zenitheesc/Probe-RAS/KiCad_Files/shapes3D/C_0805_2012Metric.step

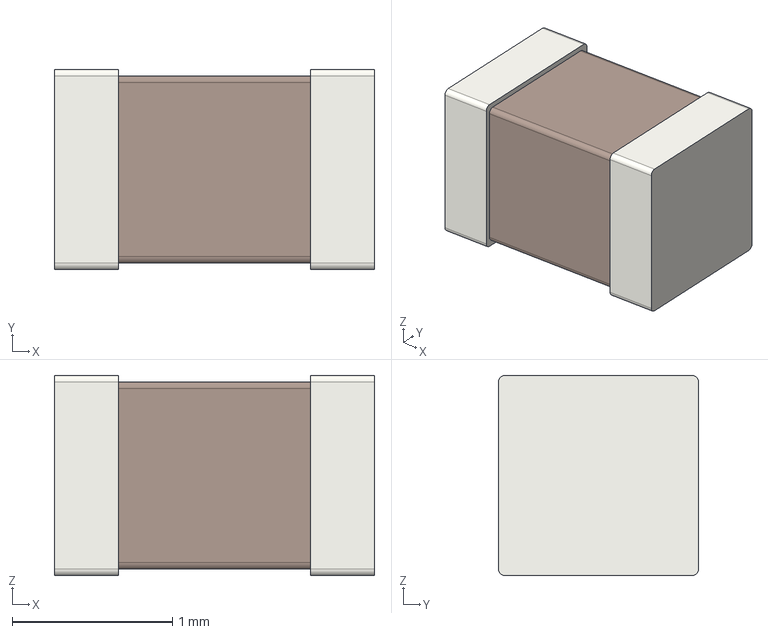
[picture p24: CAD file, 2022-01-20]
KiCad_Files/shapes3D/C_0805_2012Metric.step
2.00 x 1.25 x 1.25 mm
