zenitheesc/Probe-RAS/KiCad_Files/shapes3D/User Library-MPX5100GP.step

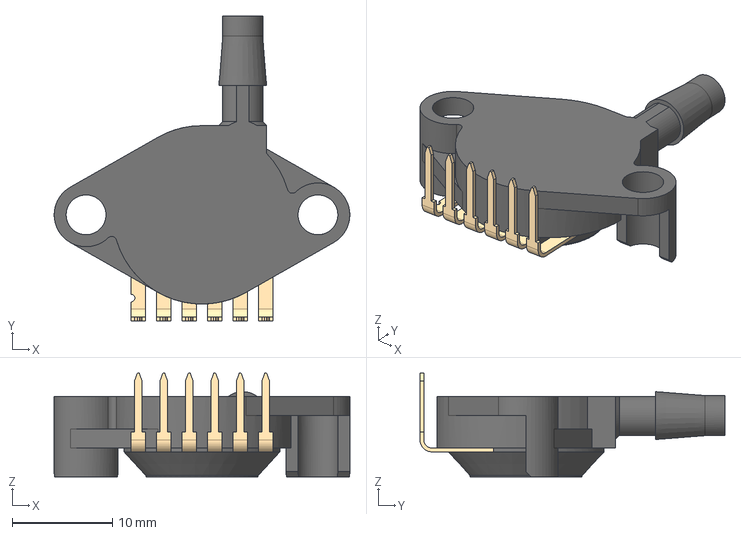
[picture p25: CAD file, 2022-01-20]
KiCad_Files/shapes3D/User Library-MPX5100GP.step
29.5 x 30.4 x 10.3 mm
