zenitheesc/Probe-RAS/KiCad_Files/shapes3D/QFN-24-1EP_4x4mm_P0.5mm_EP2.7x2.6mm.step

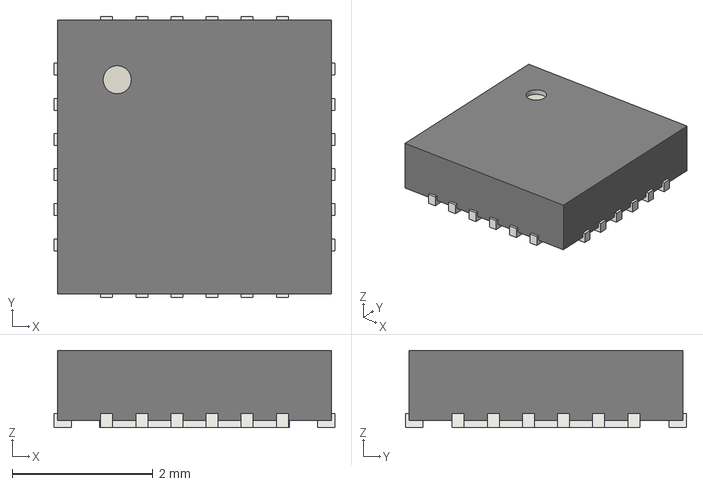
[picture p26: CAD file, 2022-01-20]
KiCad_Files/shapes3D/QFN-24-1EP_4x4mm_P0.5mm_EP2.7x2.6mm.step
4.00 x 4.00 x 1.10 mm
