zenitheesc/Probe-RAS/KiCad_Files/shapes3D/SOIC-8_3.9x4.9mm_P1.27mm.step

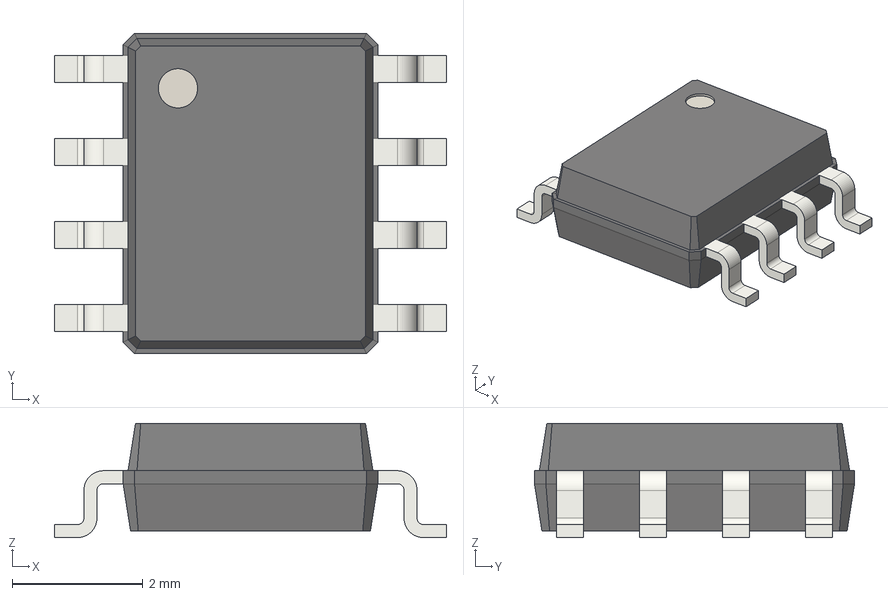
[picture p28: CAD file, 2022-01-20]
KiCad_Files/shapes3D/SOIC-8_3.9x4.9mm_P1.27mm.step
6.00 x 4.90 x 1.75 mm
