zenitheesc/Probe-RAS/KiCad_Files/shapes3D/PTS636_SM43J_SMTR_LFS.stp

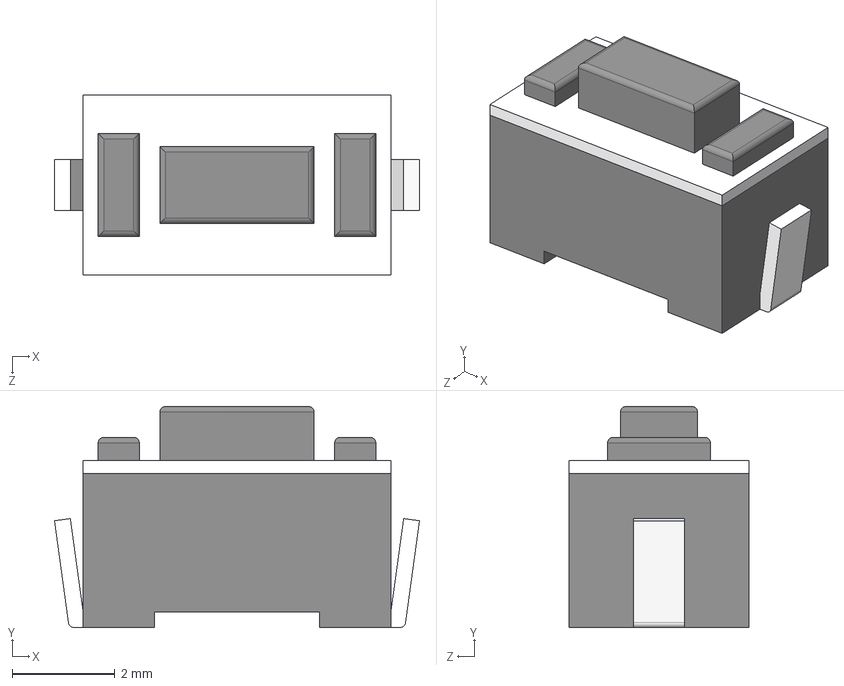
[picture p29: CAD file, 2022-01-20]
KiCad_Files/shapes3D/PTS636_SM43J_SMTR_LFS.stp
7.10 x 4.30 x 3.50 mm
